seco/ESP8266_IM_MESSAGE_DISPLAY/bitmaps/output.jpg

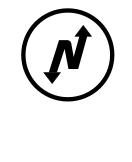
bitmaps/output.jpg
