seco/ESP8266_IM_MESSAGE_DISPLAY/pics/9bit_spi_transfer.png

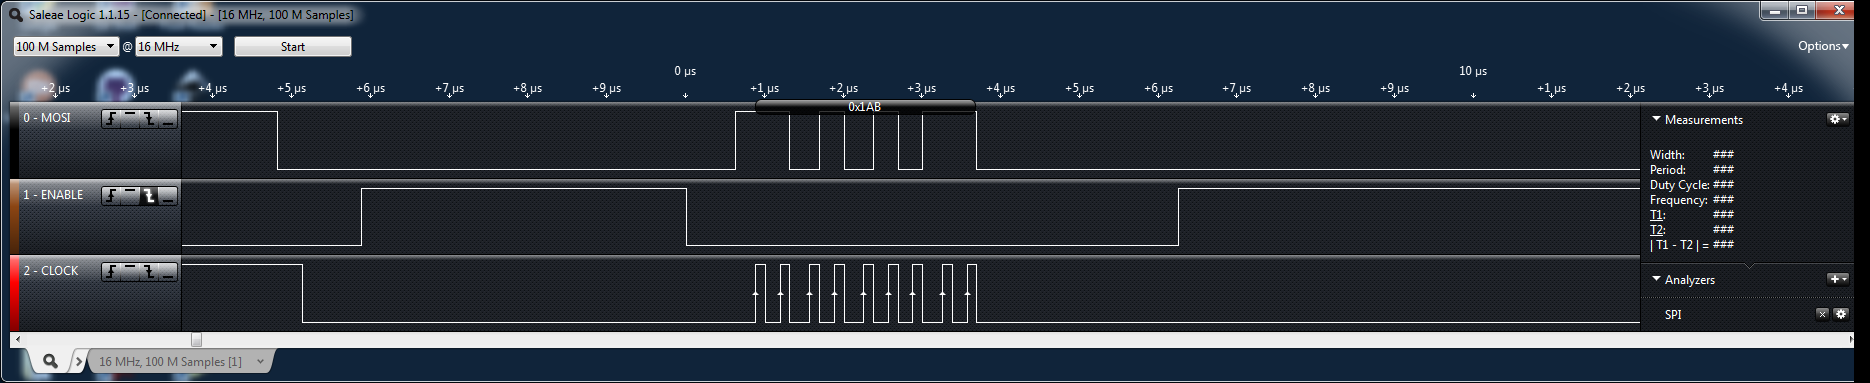
pics/9bit_spi_transfer.png
