seco/ESP8266_IM_MESSAGE_DISPLAY/pics/burn_settings.jpg

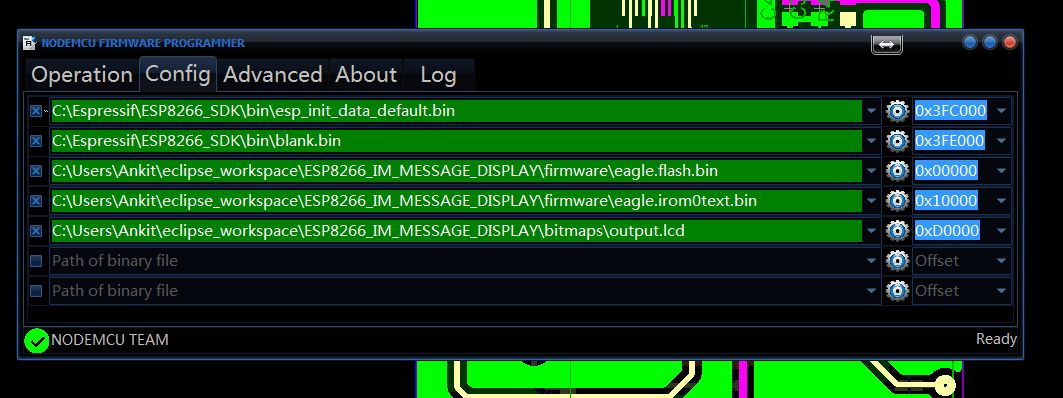
pics/burn_settings.jpg
