seco/ESP8266_IM_MESSAGE_DISPLAY/pics/IMG_20161025_234421.jpg

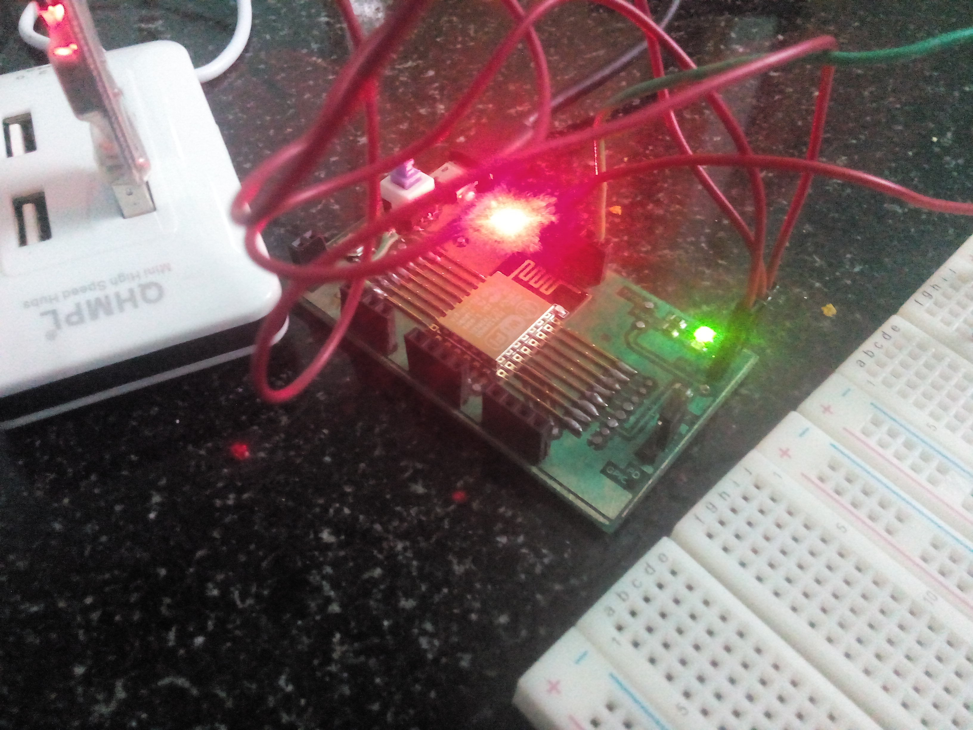
pics/IMG_20161025_234421.jpg
