seco/ESP8266_IM_MESSAGE_DISPLAY/pics/IMG_20161027_233724.jpg

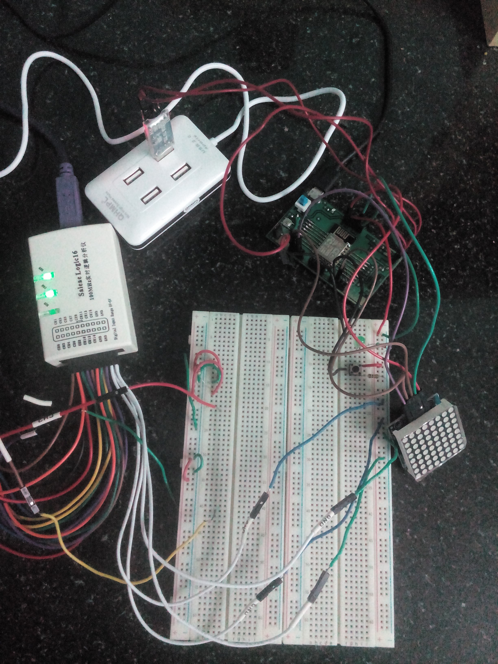
pics/IMG_20161027_233724.jpg
