seco/ESP8266_IM_MESSAGE_DISPLAY/pics/IMG_20161101_094953.jpg

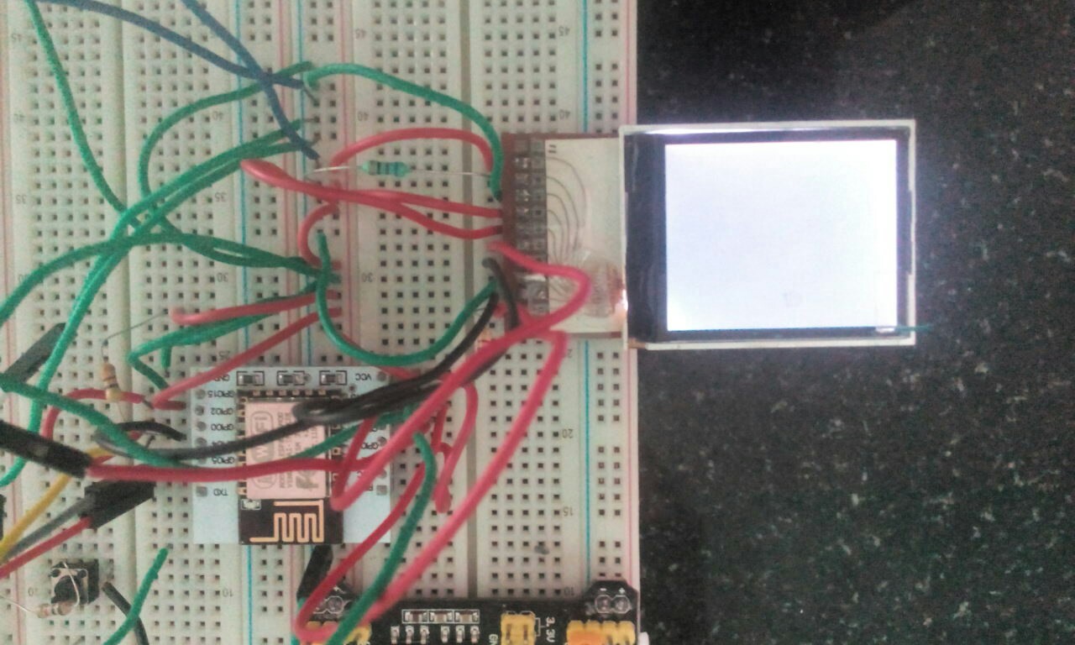
pics/IMG_20161101_094953.jpg
