seco/ESP8266_IM_MESSAGE_DISPLAY/pics/IMG_20161102_211320.jpg

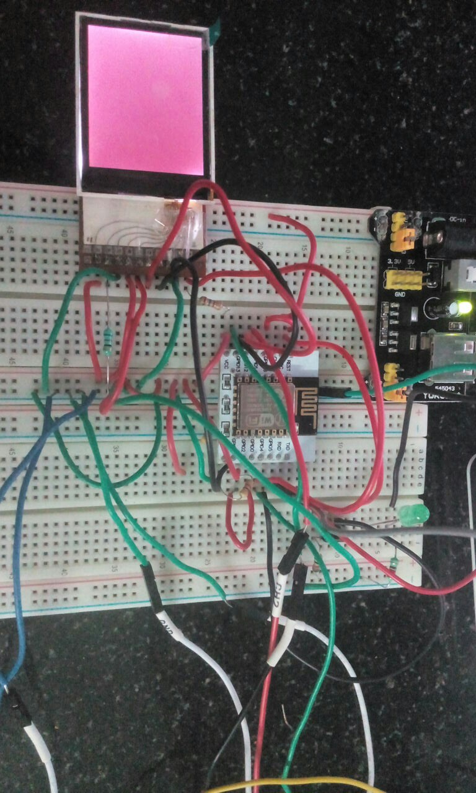
pics/IMG_20161102_211320.jpg
