seco/ESP8266_IM_MESSAGE_DISPLAY/pics/IMG_20161103_234325.jpg

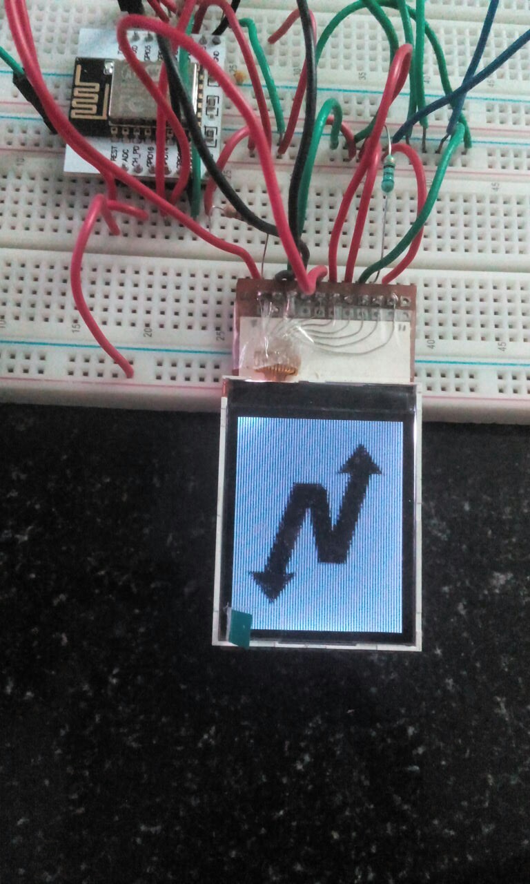
pics/IMG_20161103_234325.jpg
