seco/ESP8266_IM_MESSAGE_DISPLAY/pics/IMG_20161105_124945.jpg

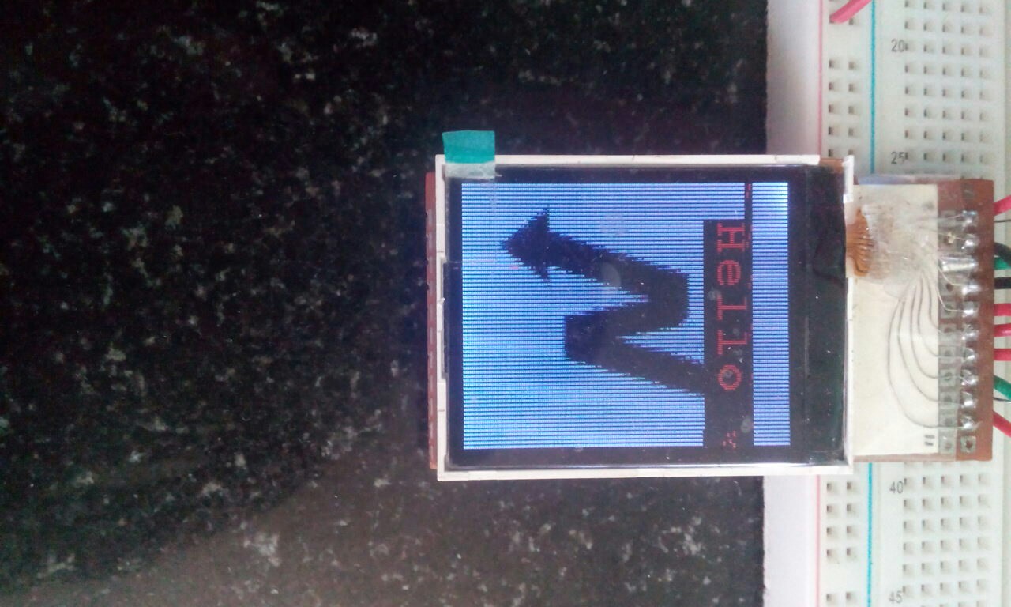
pics/IMG_20161105_124945.jpg
