seco/ESP8266_IM_MESSAGE_DISPLAY/pics/IMG_20161105_200241.jpg

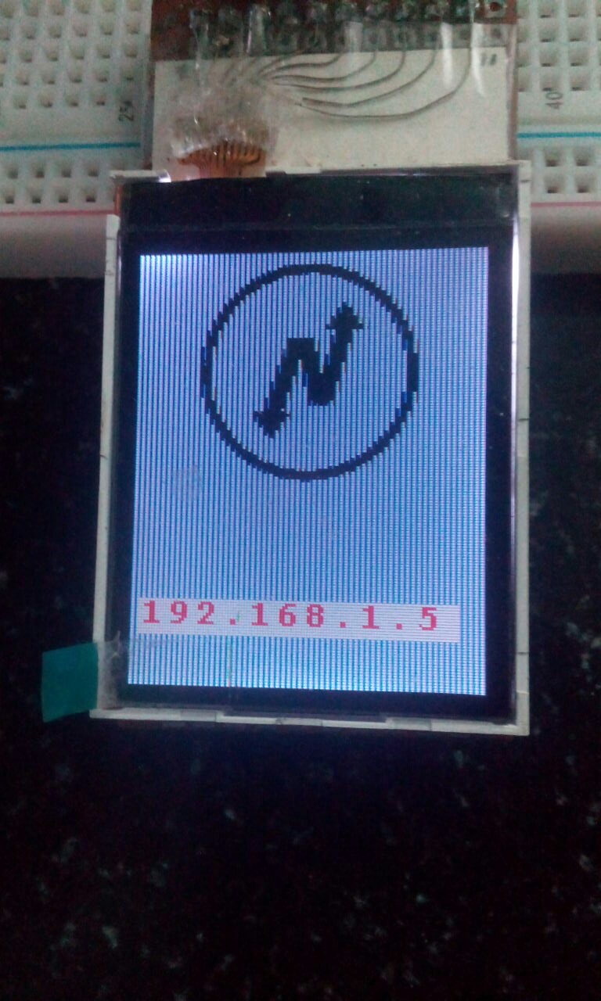
pics/IMG_20161105_200241.jpg
