seco/ESP8266_IM_MESSAGE_DISPLAY/pics/IMG_20161105_212802.jpg

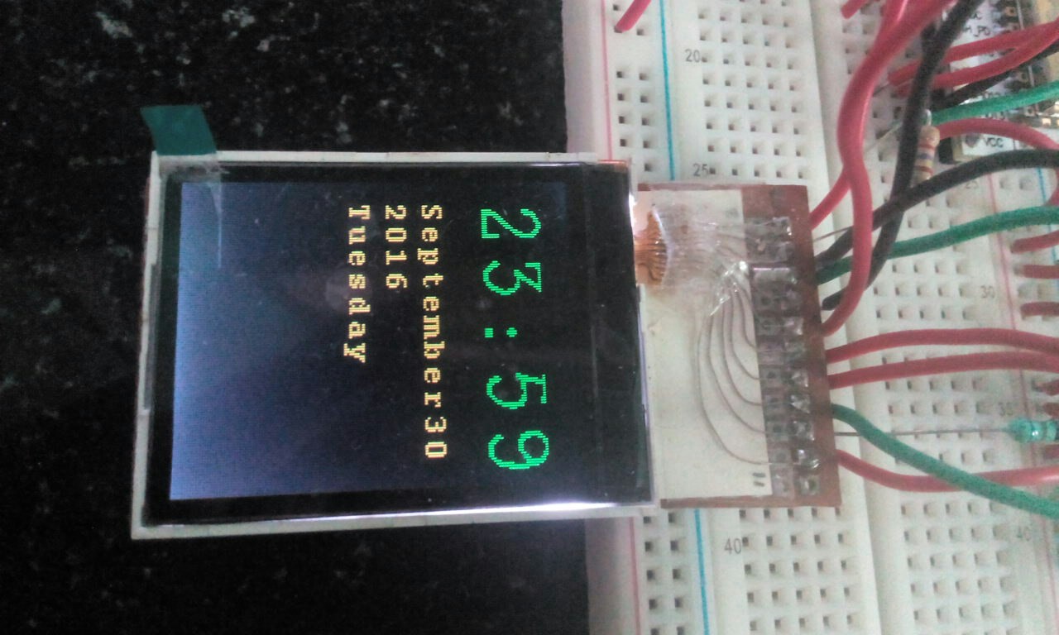
pics/IMG_20161105_212802.jpg
