seco/ESP8266_IM_MESSAGE_DISPLAY/pics/IMG_20161106_002323.jpg

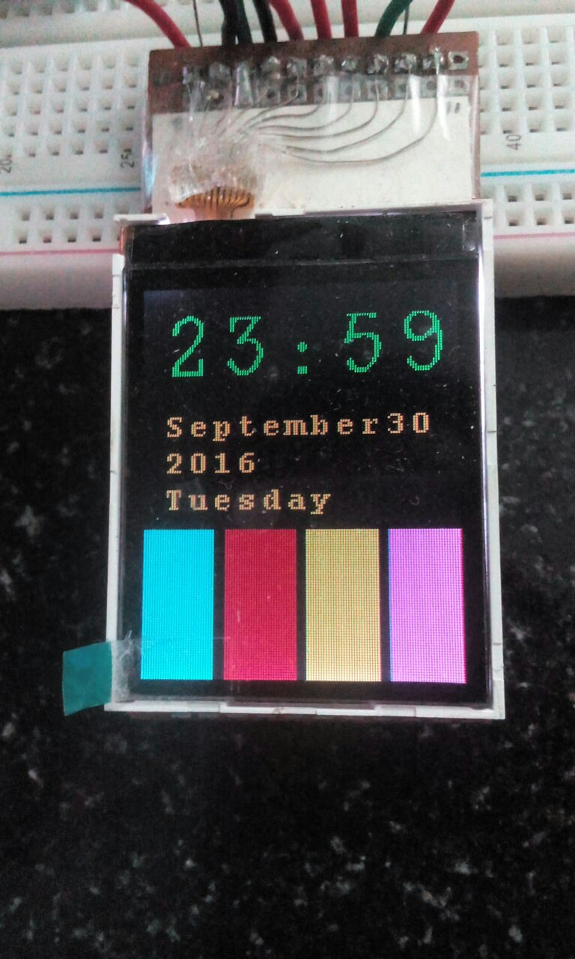
pics/IMG_20161106_002323.jpg
