seco/ESP8266_IM_MESSAGE_DISPLAY/pics/IMG_20161106_003747.jpg

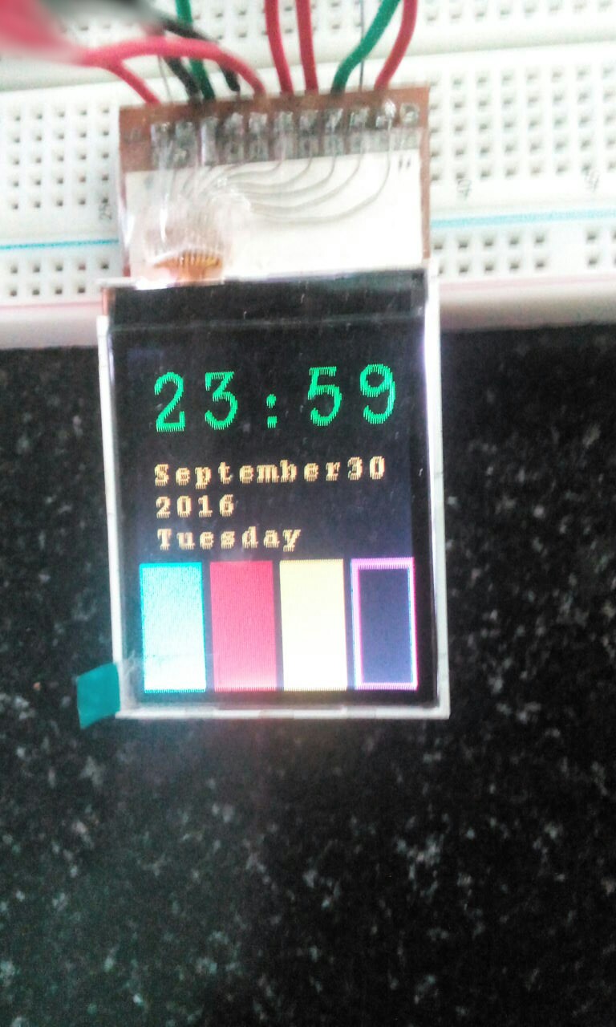
pics/IMG_20161106_003747.jpg
