seco/ESP8266_IM_MESSAGE_DISPLAY/pics/IMG_20161106_125553.jpg

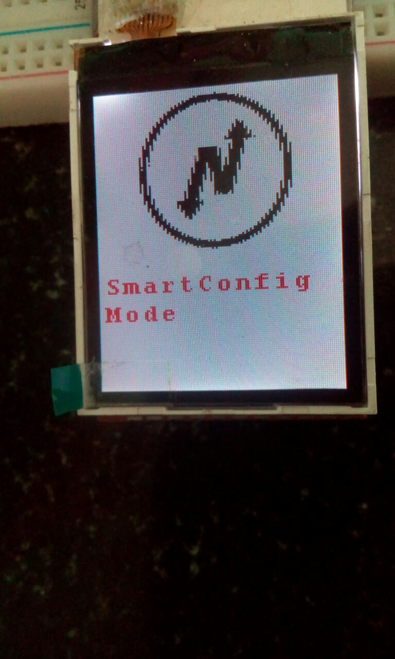
pics/IMG_20161106_125553.jpg
