seco/ESP8266_IM_MESSAGE_DISPLAY/pics/IMG_20161109_203425.jpg

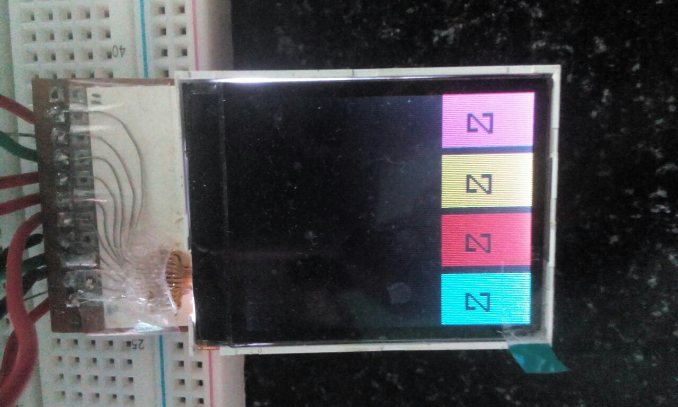
pics/IMG_20161109_203425.jpg
