seco/ESP8266_IM_MESSAGE_DISPLAY/pics/IMG_20161111_015646.jpg

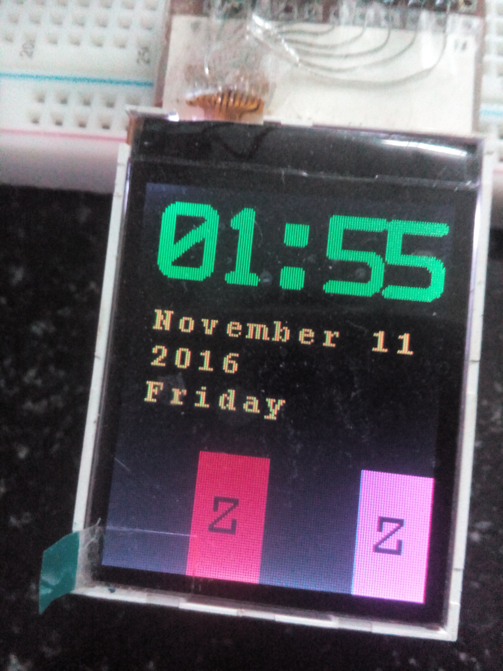
pics/IMG_20161111_015646.jpg
