seco/ESP8266_IM_MESSAGE_DISPLAY/pics/IMG_20161112_005316.jpg

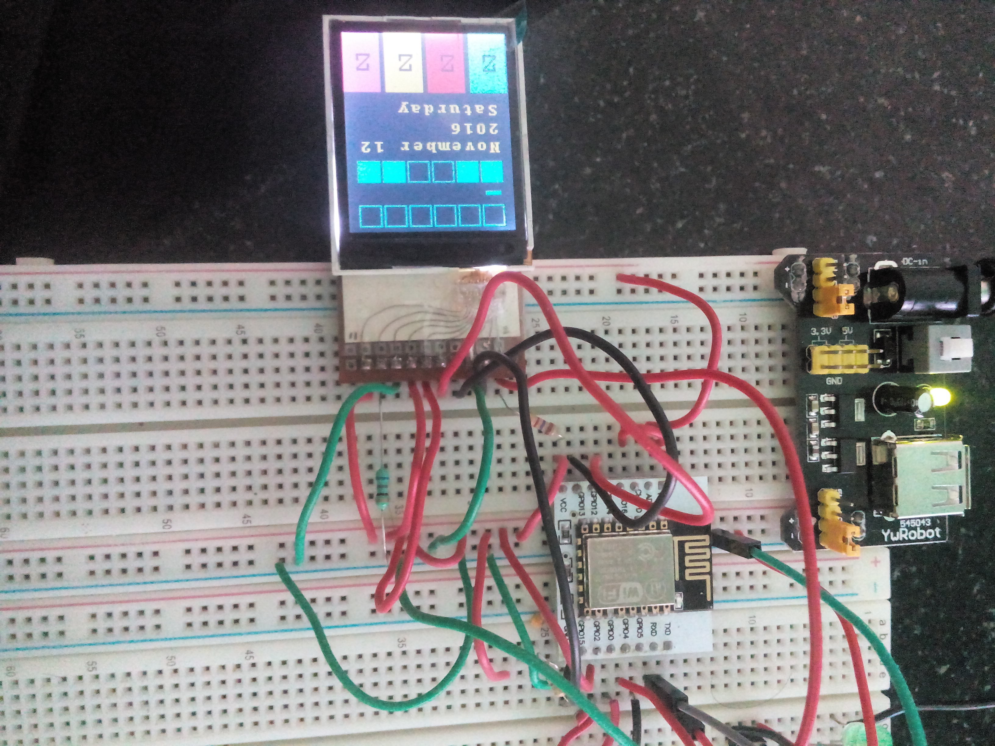
pics/IMG_20161112_005316.jpg
