seco/ESP8266_IM_MESSAGE_DISPLAY/pics/IMG_20161112_012728.jpg

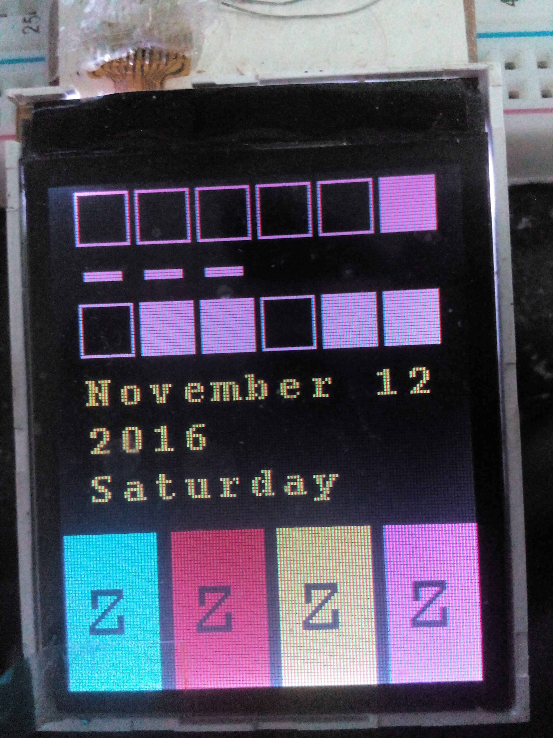
pics/IMG_20161112_012728.jpg
