seco/ESP8266_IM_MESSAGE_DISPLAY/pics/IMG_20161112_020354.jpg

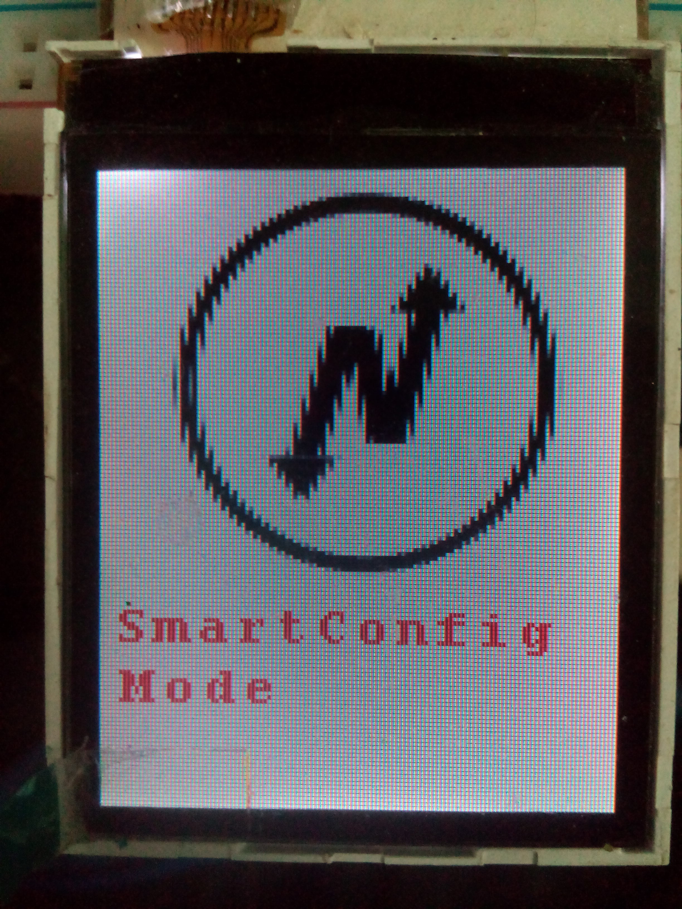
pics/IMG_20161112_020354.jpg
