seco/ESP8266_IM_MESSAGE_DISPLAY/pics/IMG_20161211_225113 (1).jpg

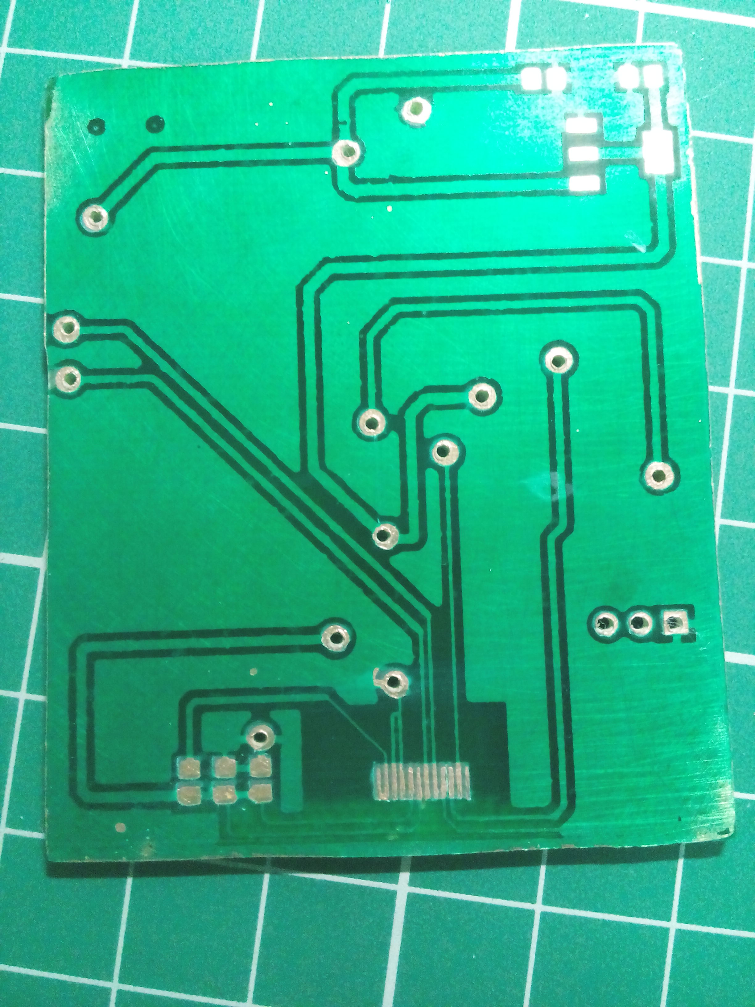
pics/IMG_20161211_225113 (1).jpg
