seco/ESP8266_IM_MESSAGE_DISPLAY/pics/IMG_20161211_225122.jpg

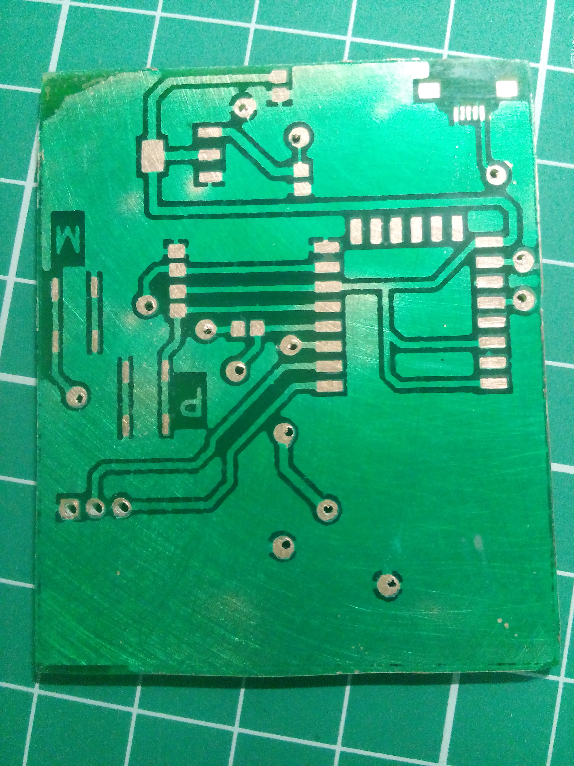
pics/IMG_20161211_225122.jpg
