seco/ESP8266_IM_MESSAGE_DISPLAY/pics/IMG_20161213_000751.jpg

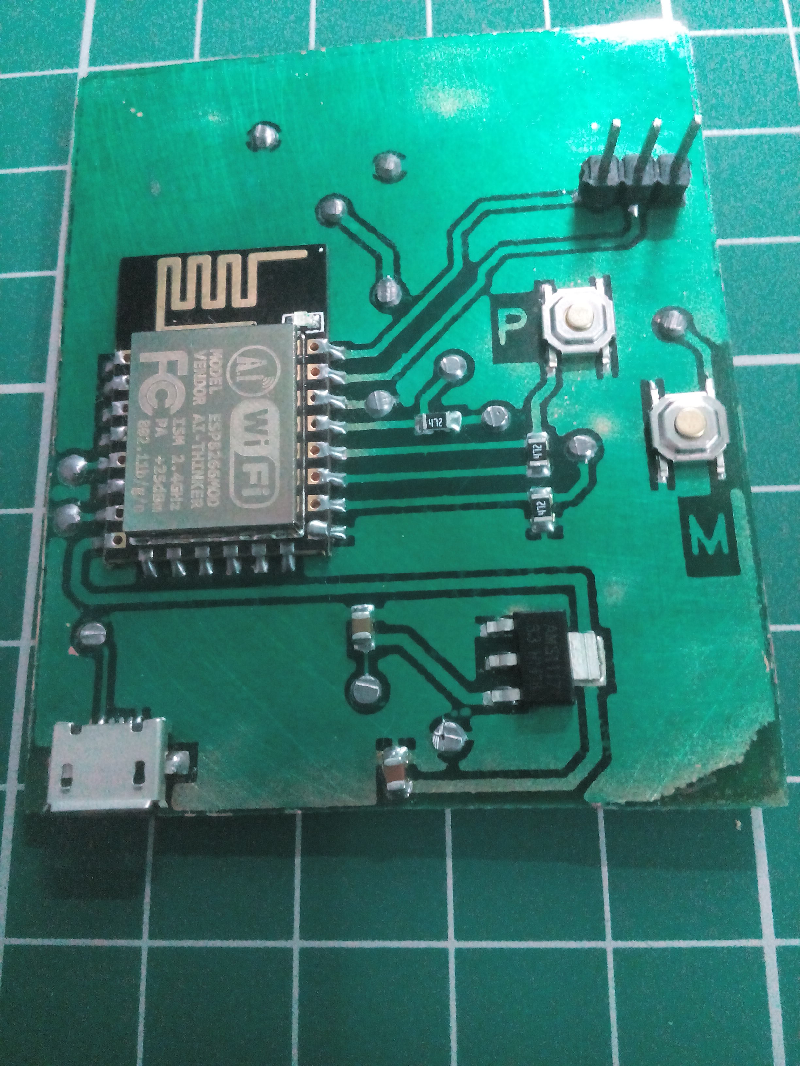
pics/IMG_20161213_000751.jpg
