seco/ESP8266_IM_MESSAGE_DISPLAY/pics/IMG_20161214_202654.jpg

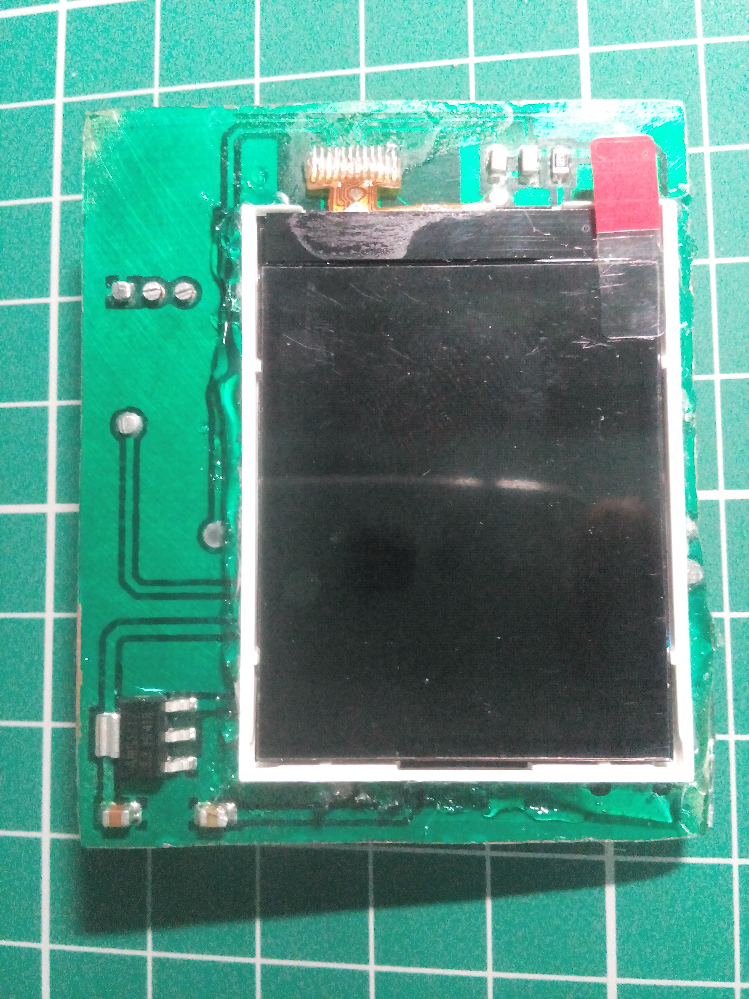
pics/IMG_20161214_202654.jpg
