seco/ESP8266_IM_MESSAGE_DISPLAY/pics/IMG_20161215_195828.jpg

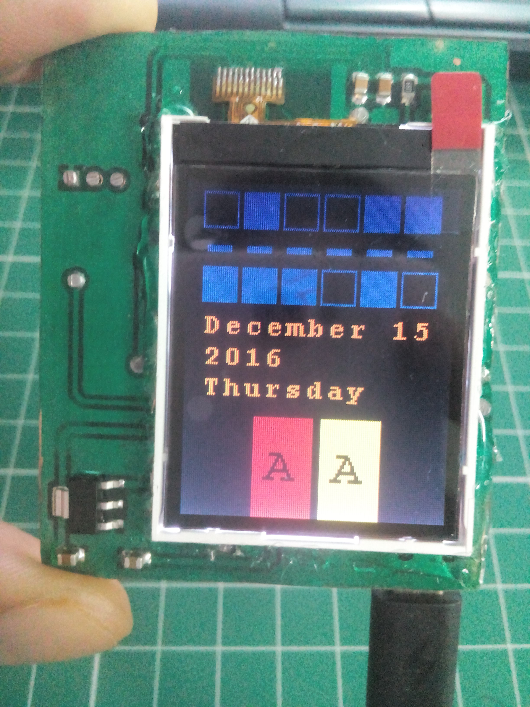
pics/IMG_20161215_195828.jpg
