seco/ESP8266_IM_MESSAGE_DISPLAY/pics/pcb2.jpg

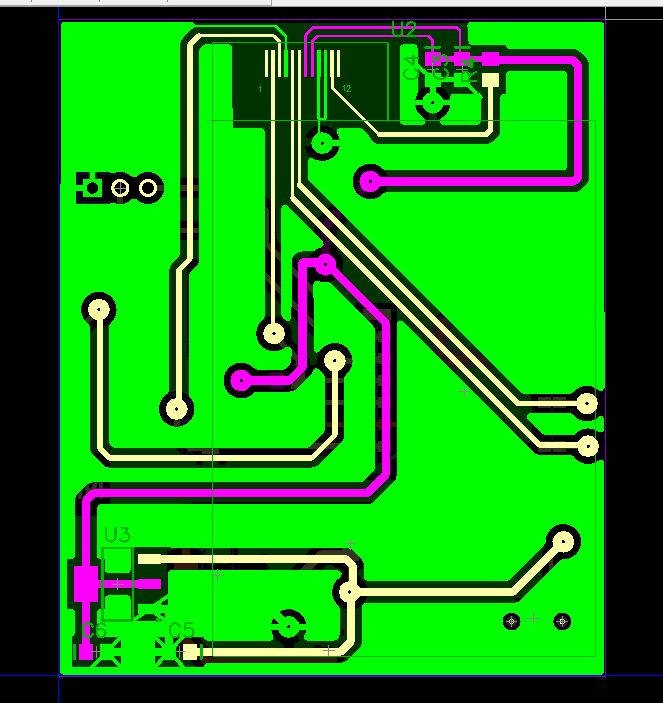
pics/pcb2.jpg
