seco/ESP8266_IM_MESSAGE_DISPLAY/pics/spi_screenshot.png

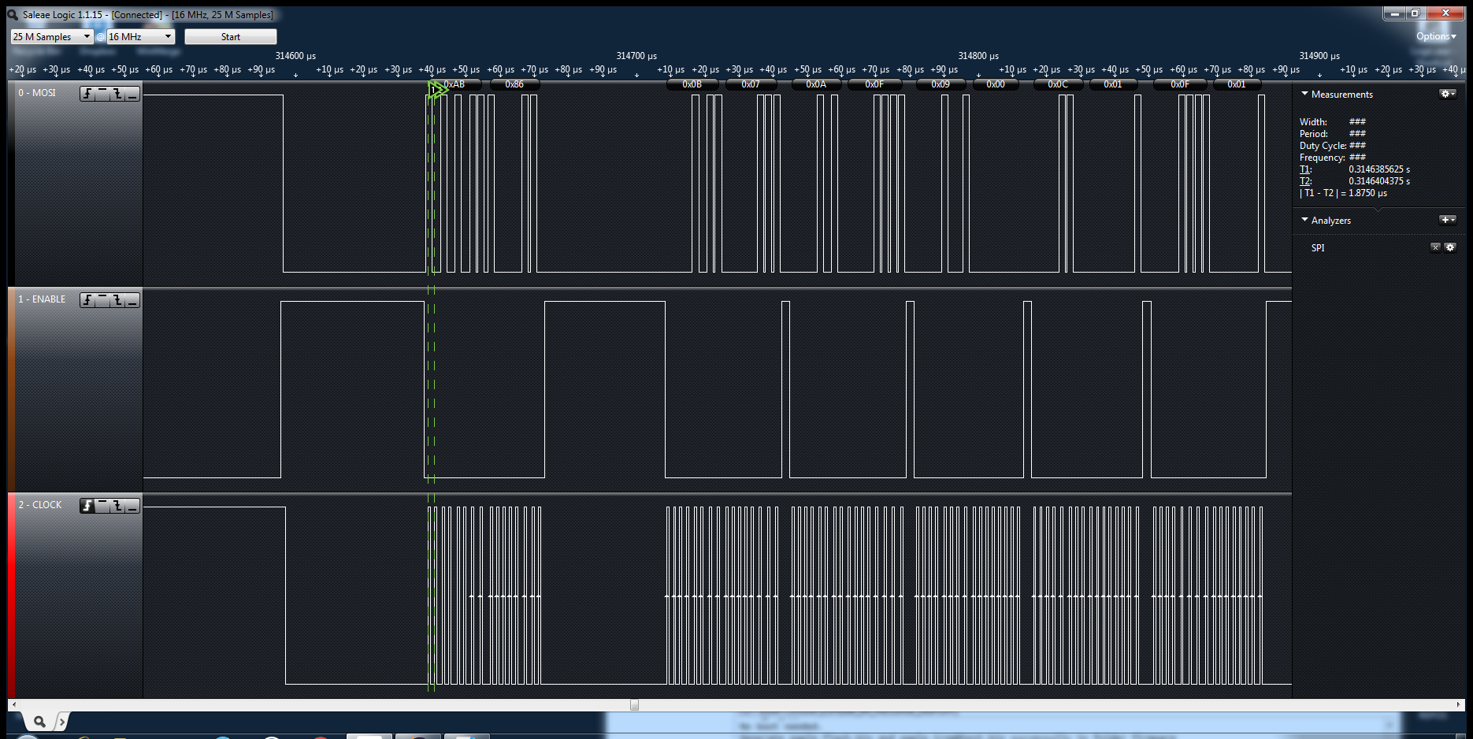
pics/spi_screenshot.png
